RetroFuturisticEngineer/RetroARDUInput/Case/STL/Case-Reset Sleeve.stl

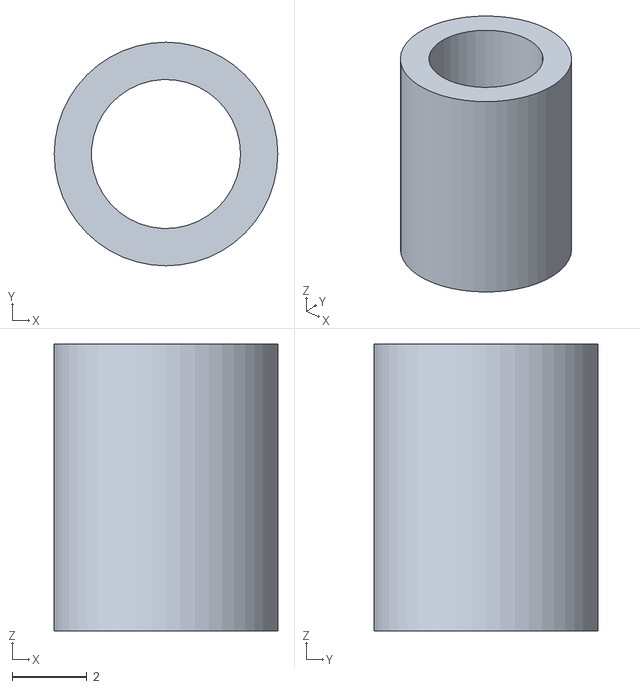
[picture p41: CAD file, 2022-08-06]
Case/STL/Case-Reset Sleeve.stl
6.00 x 6.00 x 7.70
