RetroFuturisticEngineer/RetroARDUInput/Case/STL/02 - Case-Top Cover Emboss.stl

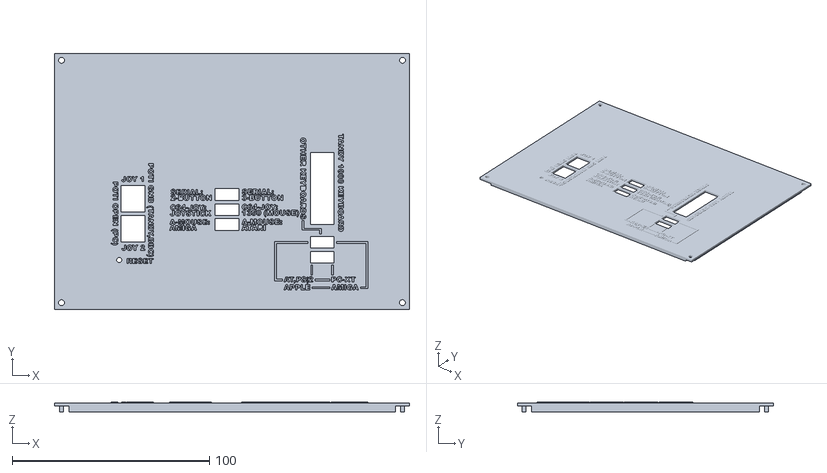
[picture p42: CAD file, 2022-08-06]
Case/STL/02 - Case-Top Cover Emboss.stl
180.0 x 130.0 x 5.00
