RetroFuturisticEngineer/RetroARDUInput/Case/STL/01 - Case-Baseplate.stl

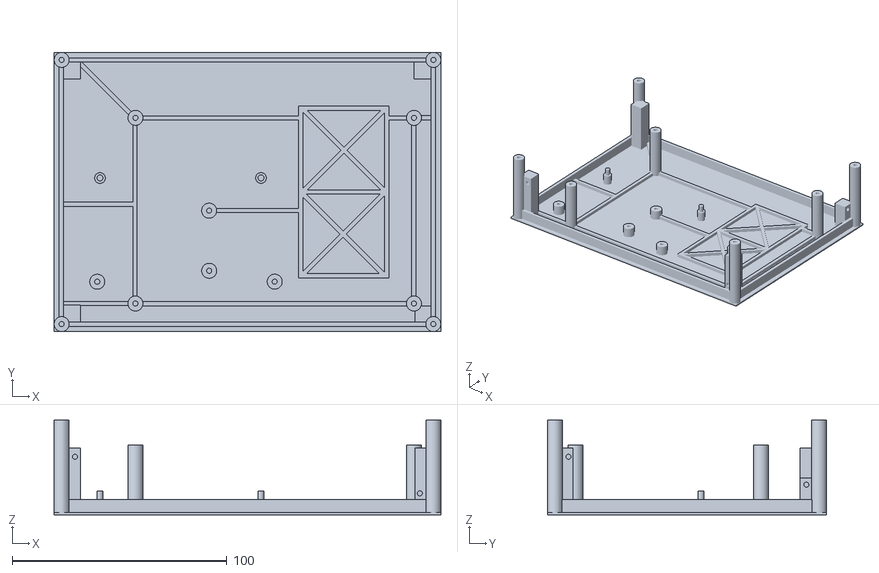
[picture p43: CAD file, 2022-08-06]
Case/STL/01 - Case-Baseplate.stl
180.0 x 130.0 x 44.0
